liaozhelin/yds-charger/3.Software/yds_charger/components/u8g2/sys/avr/avr-libc/atmega328p-hw-i2c/_20190603_194930.JPG

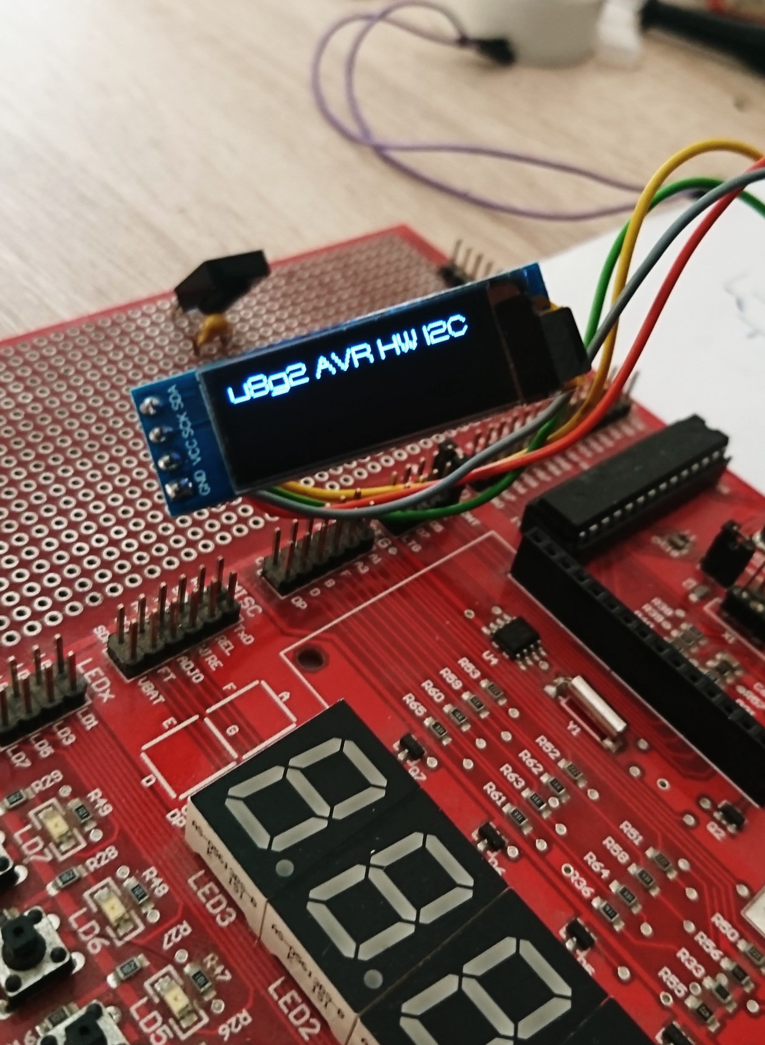
3.Software/yds_charger/components/u8g2/sys/avr/avr-libc/atmega328p-hw-i2c/_20190603_194930.JPG
