liaozhelin/yds-charger/4.Structure/otherModule/OLED/OLED TFT 0.96 inch 64x128 monochrome 01.PNG

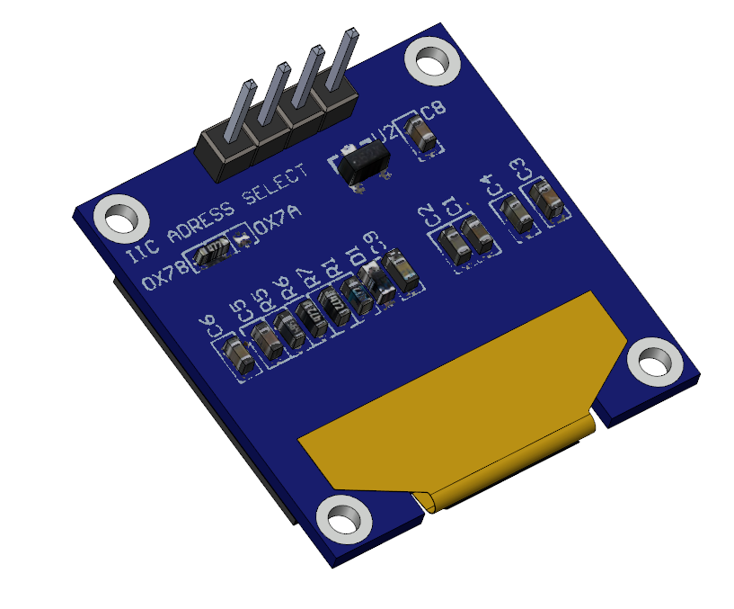
4.Structure/otherModule/OLED/OLED TFT 0.96 inch 64x128 monochrome 01.PNG
