liaozhelin/yds-charger/4.Structure/otherModule/OLED/OLED TFT 0.96 inch 64x128 monochrome 02.PNG

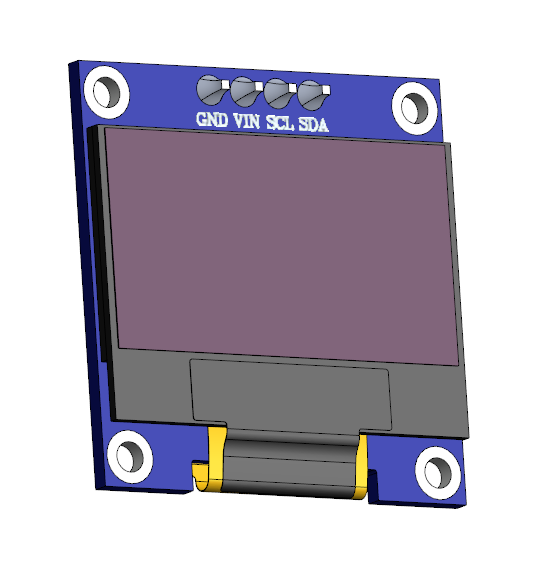
4.Structure/otherModule/OLED/OLED TFT 0.96 inch 64x128 monochrome 02.PNG
