liaozhelin/yds-charger/3.Software/yds_charger/components/ota/include/ota.h

/*
 * @Author: [LiaoZhelin]
 * @Date: 2022-05-09 21:17:30
 * @LastEditors: [LiaoZhelin]
 * @LastEditTime: 2022-05-09 22:36:39
 * @Description: 
 */
#ifndef _OTA_H_
#define _OTA_H_

void advanced_ota_example_task(void *pvParameter);
void OTA_Init(void);

#endif
